denes44/HUEnergyDisplay/datasheet/display_16mm_4_KYX-4402A_3.png

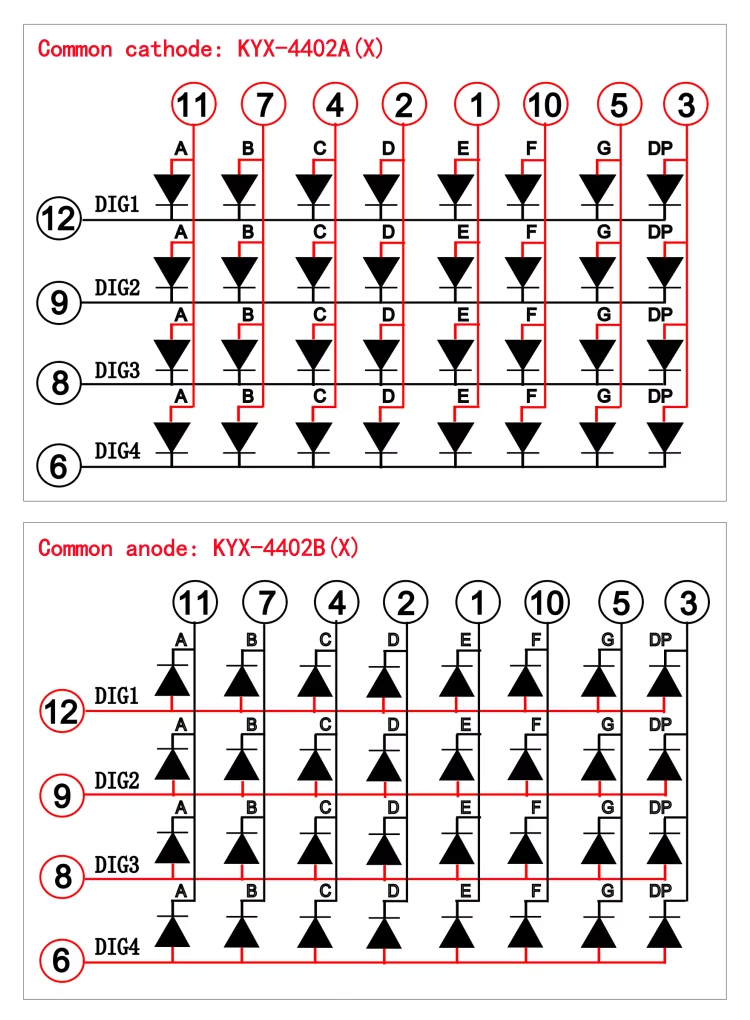
datasheet/display_16mm_4_KYX-4402A_3.png
