denes44/HUEnergyDisplay/datasheet/display_19mm_1_KYX-5261A_2.png

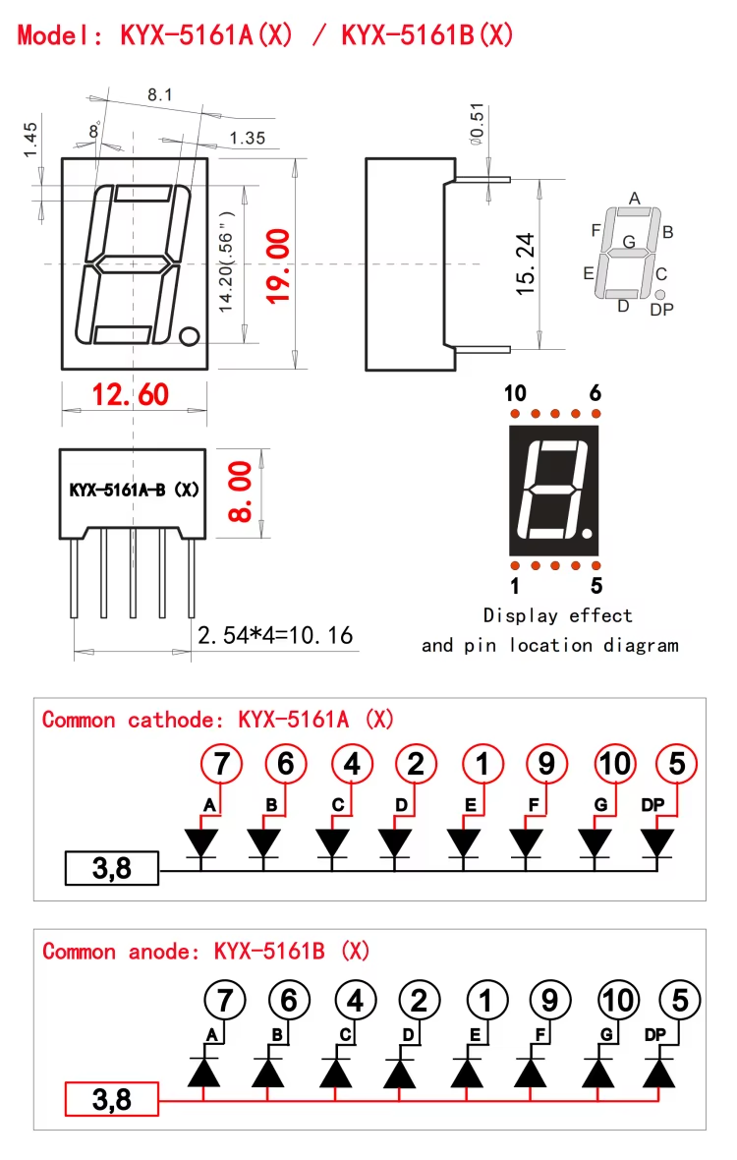
datasheet/display_19mm_1_KYX-5261A_2.png
