denes44/HUEnergyDisplay/datasheet/display_19mm_4_KYX-5461A_2.png

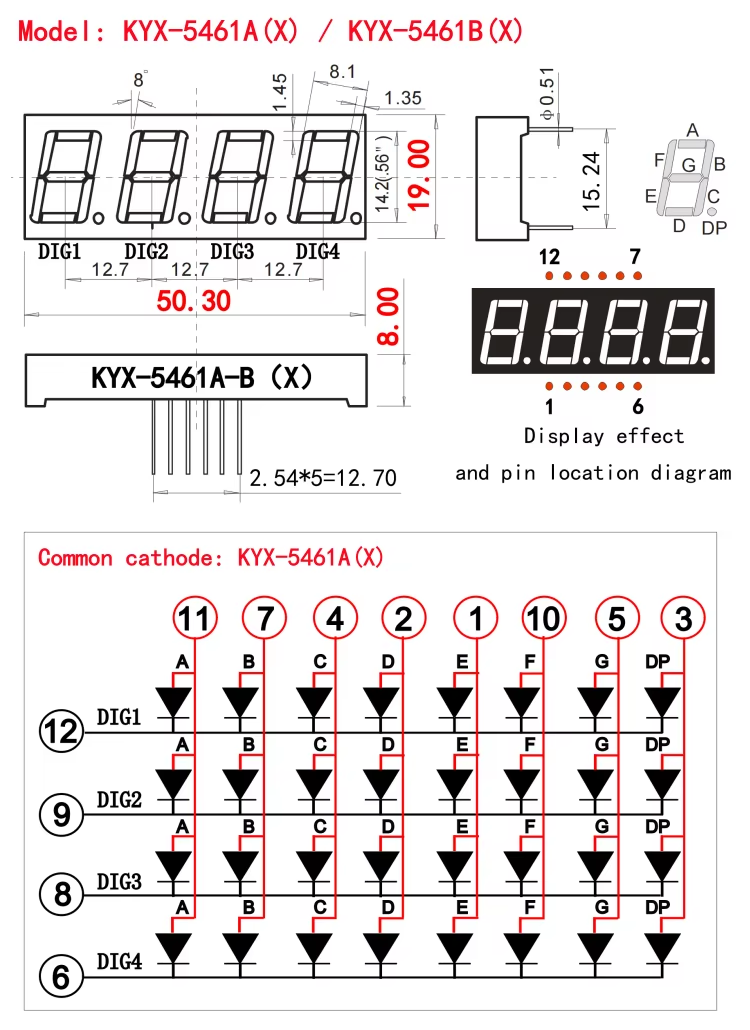
datasheet/display_19mm_4_KYX-5461A_2.png
