denes44/HUEnergyDisplay/datasheet/display_26mm_4_KYX-8401A_1.png

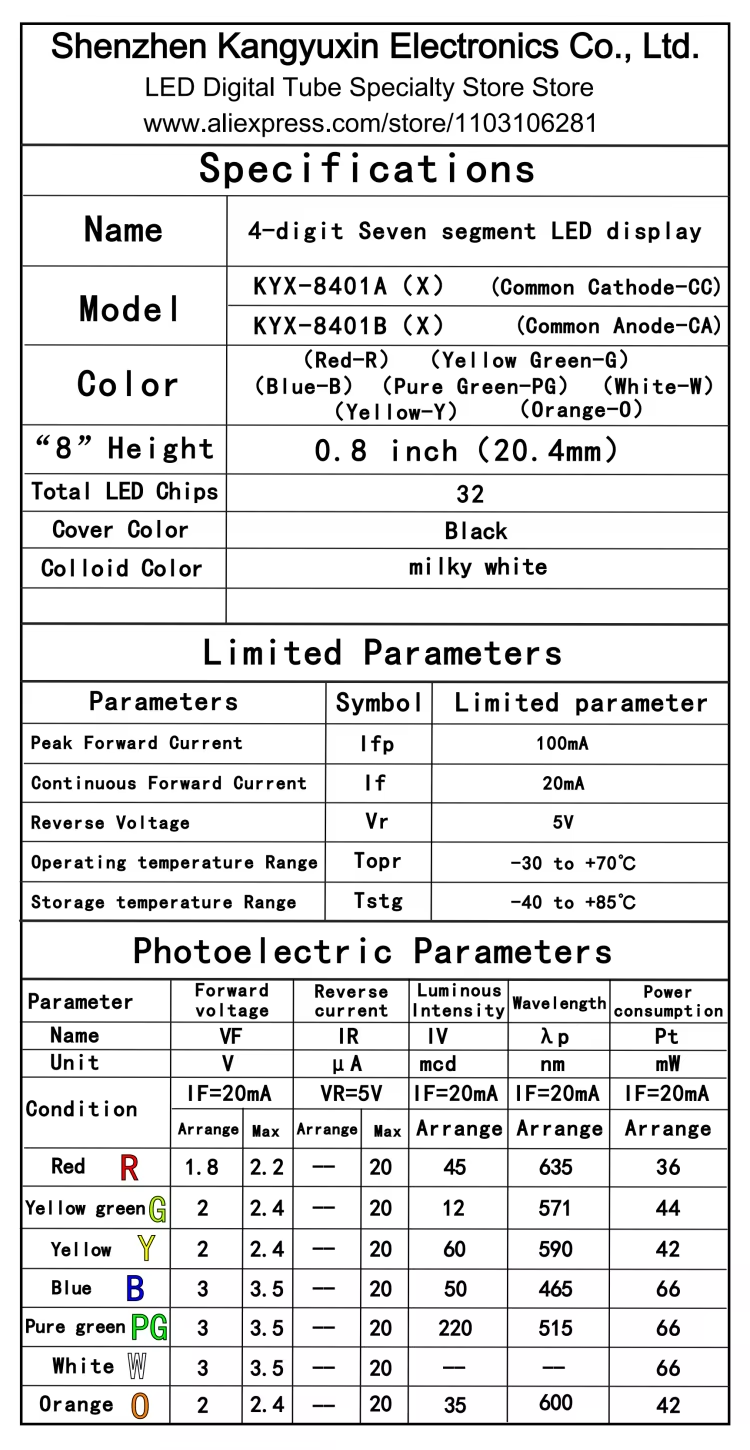
datasheet/display_26mm_4_KYX-8401A_1.png
