denes44/HUEnergyDisplay/datasheet/led_bar_8_KYX-B8(X).png

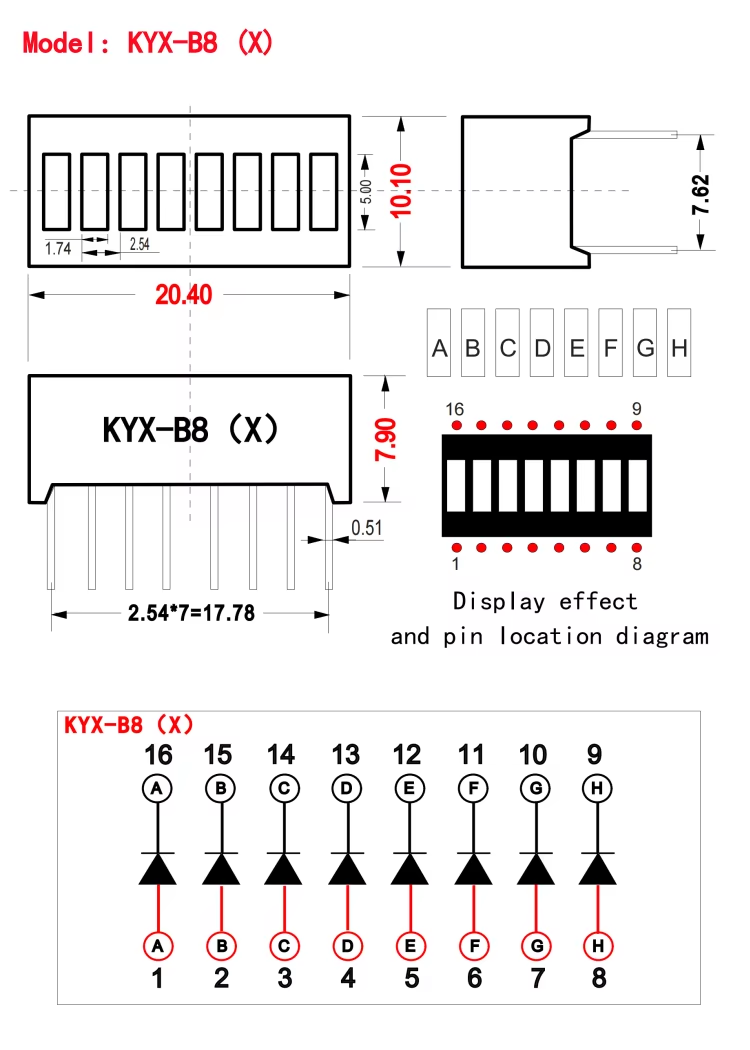
datasheet/led_bar_8_KYX-B8(X).png
